panovvv/dwm1001-devboard/renders/02_no_raytrace_back.png

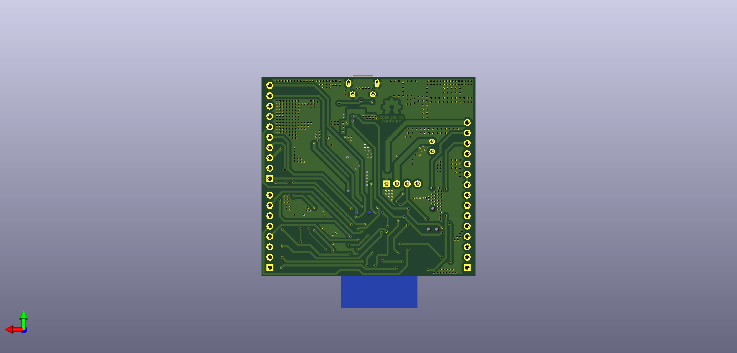
renders/02_no_raytrace_back.png
