panovvv/dwm1001-devboard/renders/03_no_raytrace_left.png

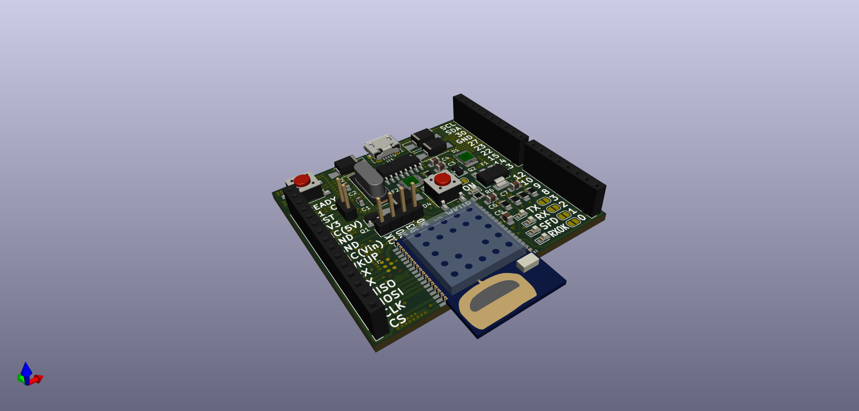
renders/03_no_raytrace_left.png
