panovvv/dwm1001-devboard/renders/04_no_raytrace_right.png

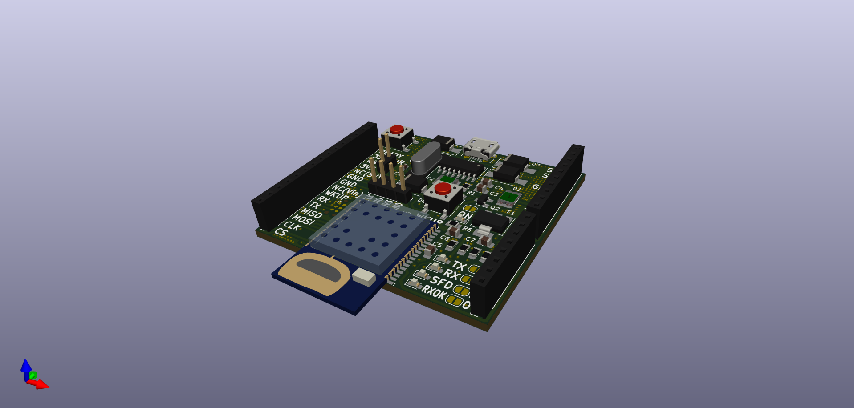
renders/04_no_raytrace_right.png
