panovvv/dwm1001-devboard/renders/09_raytrace_left.png

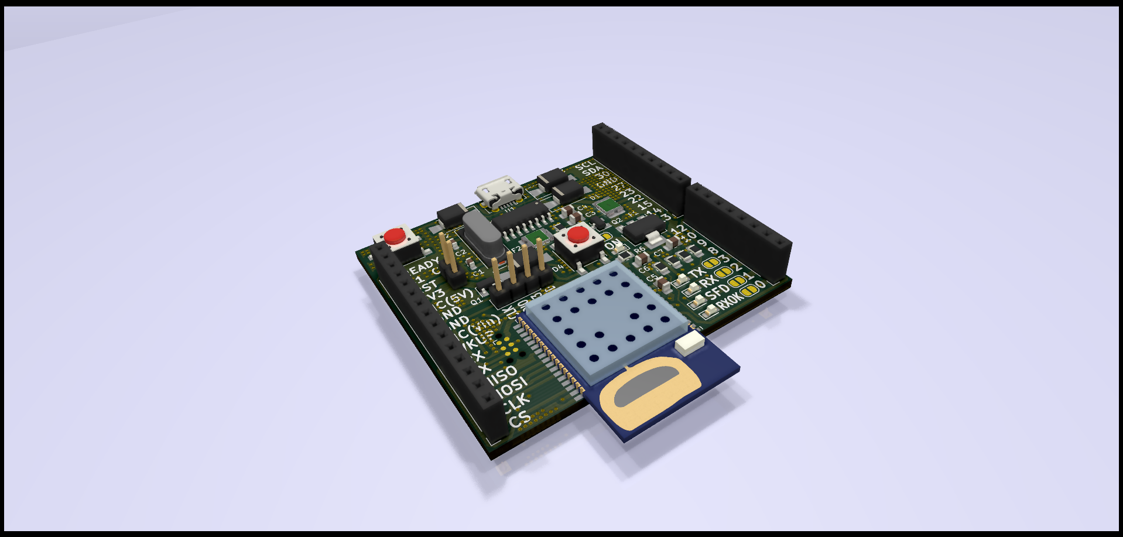
renders/09_raytrace_left.png
